doesntfazer/Quetzal/images/quetzal.jpg

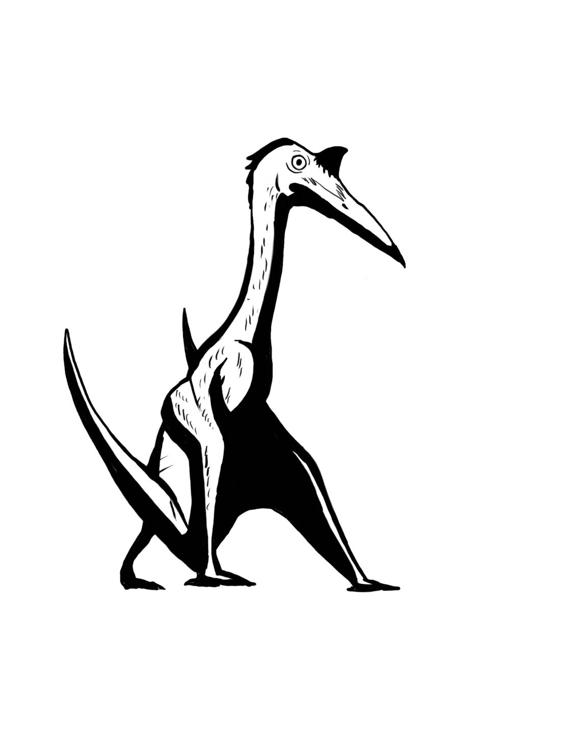
images/quetzal.jpg
